jordan-w23/Project_BOO-E/Data logger/ESP32 docs/diagrams/datalogger.png

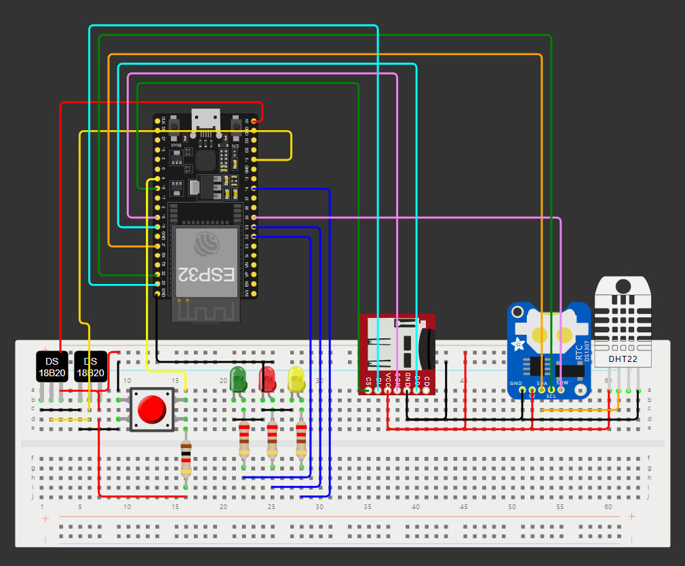
Data logger/ESP32 docs/diagrams/datalogger.png
