jordan-w23/Project_BOO-E/Data logger/ESP32 docs/diagrams/ESP32-DEV-CH340-USBC-003.jpg

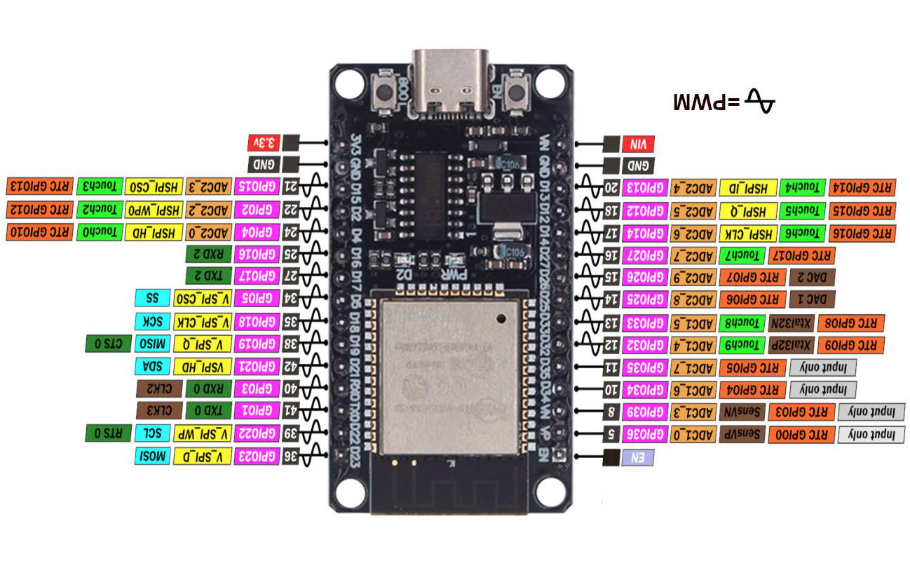
Data logger/ESP32 docs/diagrams/ESP32-DEV-CH340-USBC-003.jpg
