jordan-w23/Project_BOO-E/Data sheets/Rudder internal full.jpg

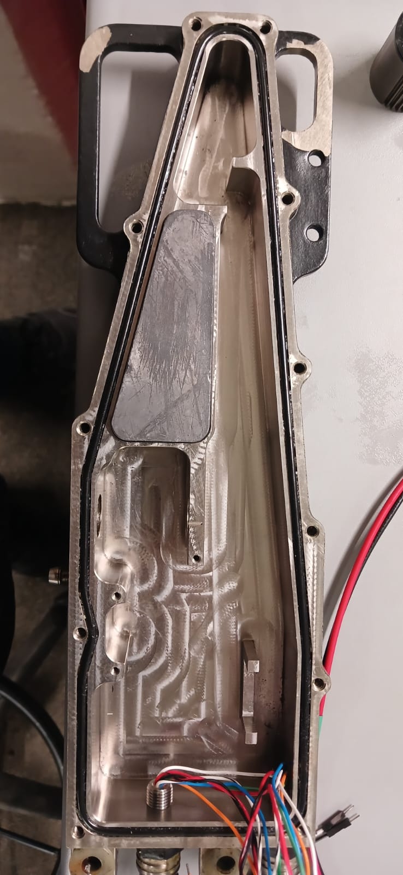
Data sheets/Rudder internal full.jpg
