jordan-w23/Project_BOO-E/Data sheets/Rudder internal ruller.jpg

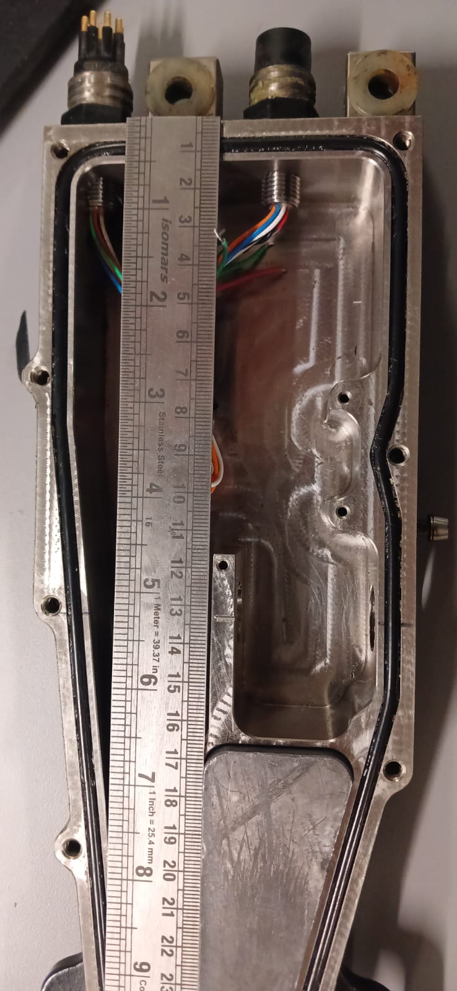
Data sheets/Rudder internal ruller.jpg
