jordan-w23/Project_BOO-E/Data sheets/Rudder internal.jpg

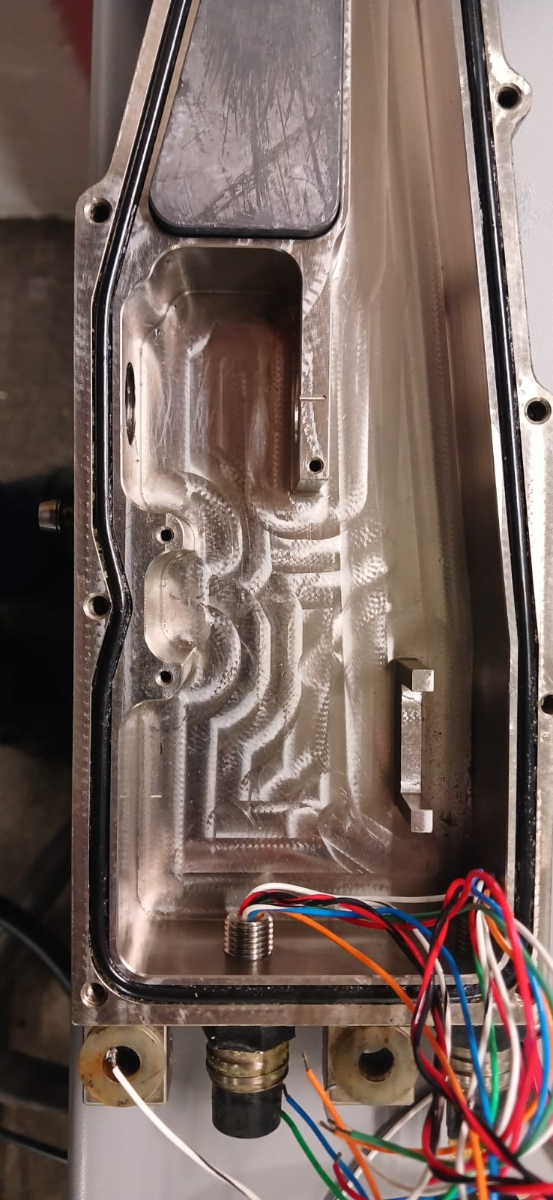
Data sheets/Rudder internal.jpg
