jordan-w23/Project_BOO-E/Pictures/BOO-E/IMG-20241016-WA0007.jpg

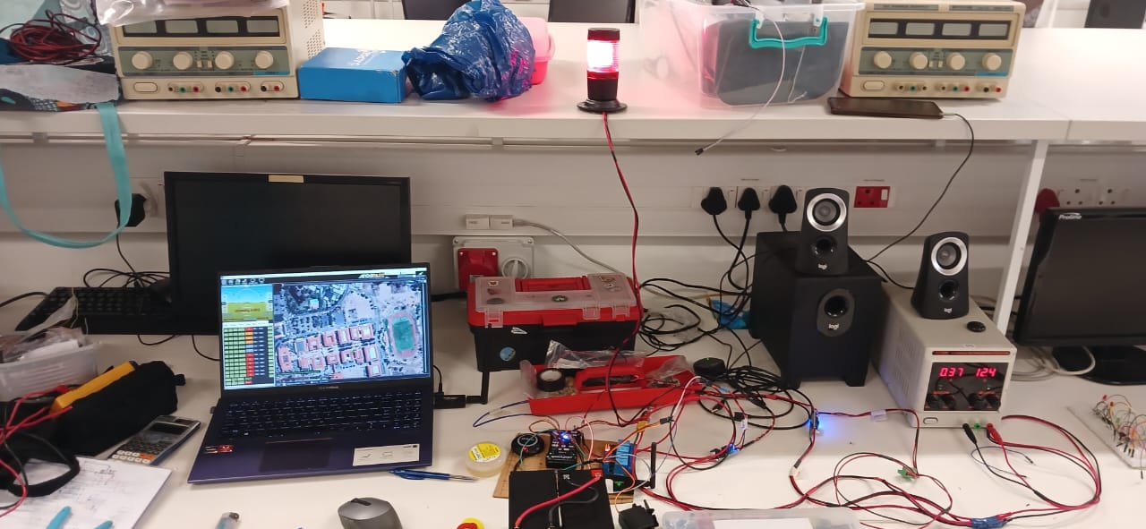
Pictures/BOO-E/IMG-20241016-WA0007.jpg
