jordan-w23/Project_BOO-E/Pictures/BOO-E/WhatsApp Image 2024-09-15 at 20.39.04_3f09f6b3.jpg

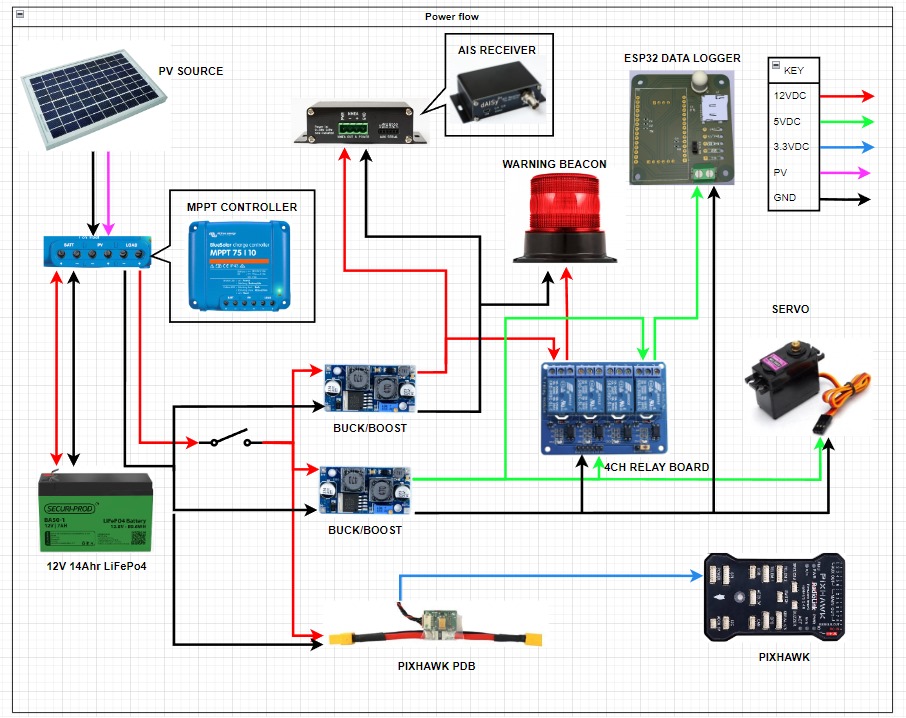
Pictures/BOO-E/WhatsApp Image 2024-09-15 at 20.39.04_3f09f6b3.jpg
