jordan-w23/Project_BOO-E/Pictures/BOO-E/WhatsApp Image 2024-10-16 at 18.33.03_7184913c.jpg

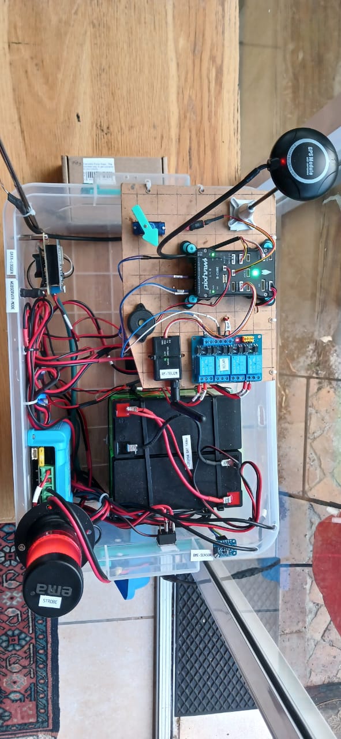
Pictures/BOO-E/WhatsApp Image 2024-10-16 at 18.33.03_7184913c.jpg
