jordan-w23/Project_BOO-E/Pictures/BOO-E/WhatsApp Image 2024-10-16 at 18.33.04_672b4f92.jpg

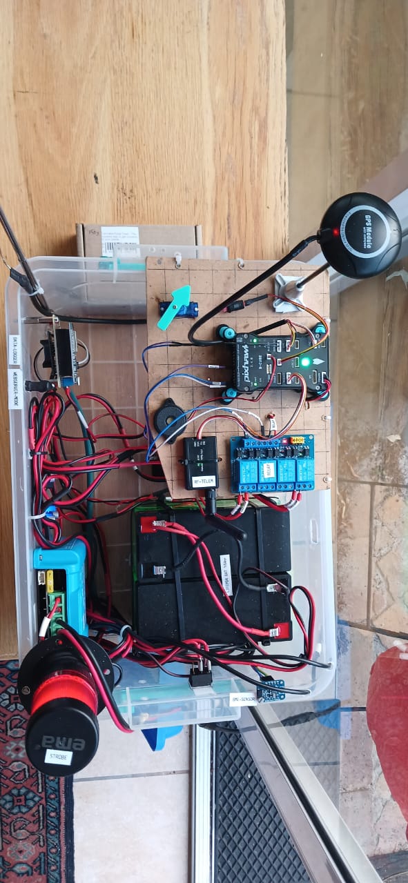
Pictures/BOO-E/WhatsApp Image 2024-10-16 at 18.33.04_672b4f92.jpg
