jordan-w23/Project_BOO-E/Pictures/BOO-E/WhatsApp Image 2024-10-17 at 18.35.57_54fe8b64.jpg

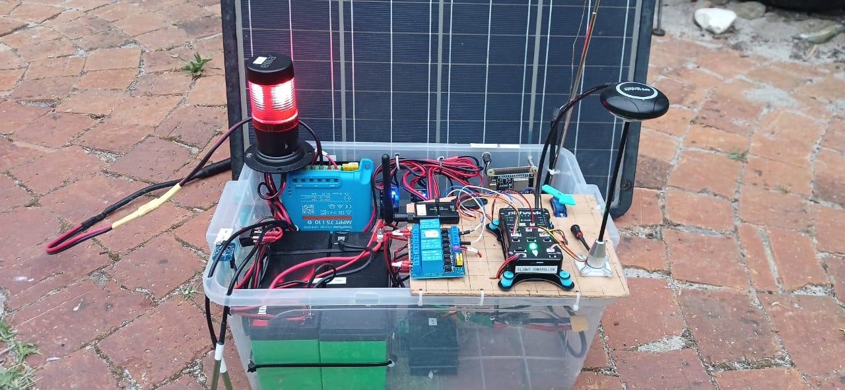
Pictures/BOO-E/WhatsApp Image 2024-10-17 at 18.35.57_54fe8b64.jpg
