jordan-w23/Project_BOO-E/Pictures/BOO-E/WhatsApp Image 2024-10-17 at 18.35.57_cdbaec98.jpg

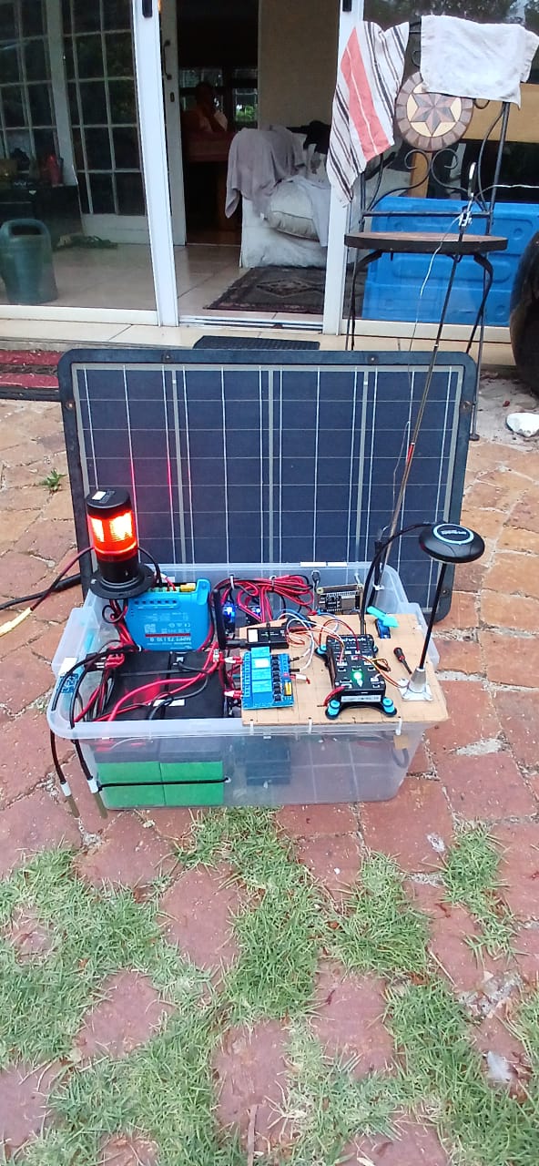
Pictures/BOO-E/WhatsApp Image 2024-10-17 at 18.35.57_cdbaec98.jpg
