jordan-w23/Project_BOO-E/Pictures/Data logger/IMG-20241016-WA0013.jpg

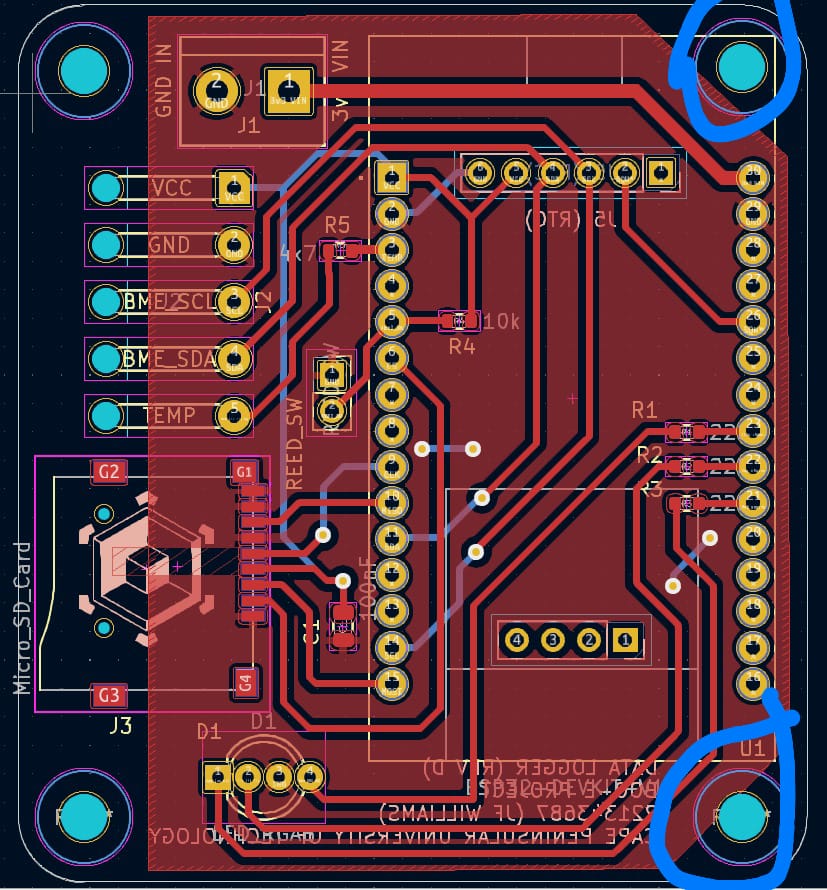
Pictures/Data logger/IMG-20241016-WA0013.jpg
