jordan-w23/Project_BOO-E/Pictures/GCS pixhawk/cf1507b16e4d5ccd977404383e6bbf5c3c93ac16.jpg

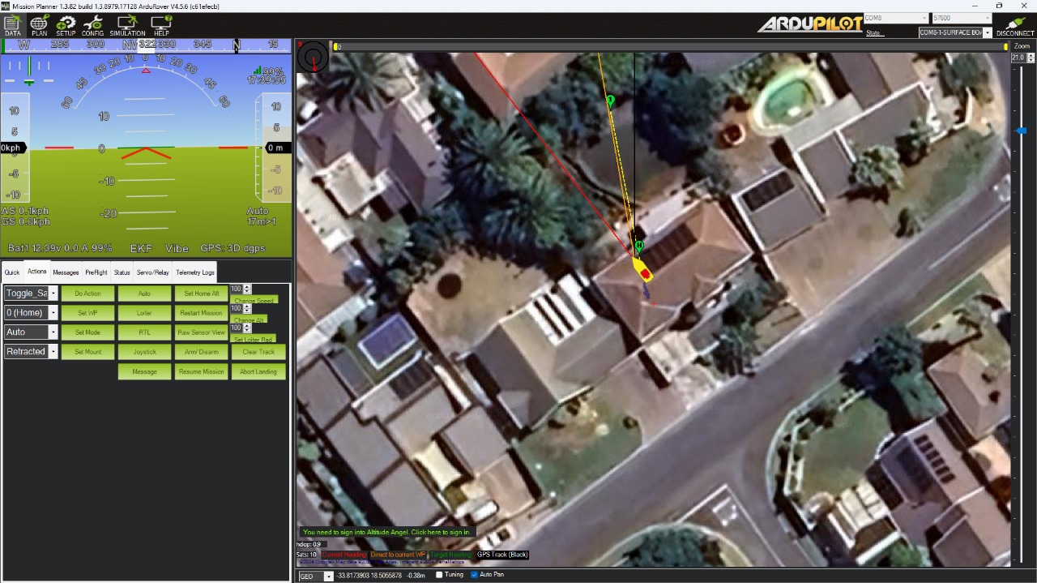
Pictures/GCS pixhawk/cf1507b16e4d5ccd977404383e6bbf5c3c93ac16.jpg
