jordan-w23/Project_BOO-E/Pictures/GCS pixhawk/IMG-20241016-WA0003.jpg

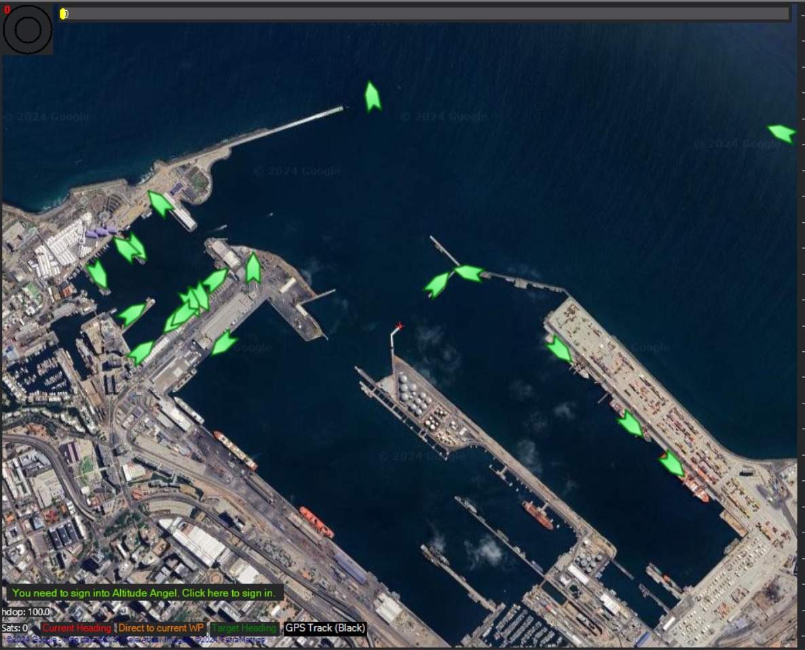
Pictures/GCS pixhawk/IMG-20241016-WA0003.jpg
