jordan-w23/Project_BOO-E/Pictures/GCS pixhawk/Left WP GSC.jpg

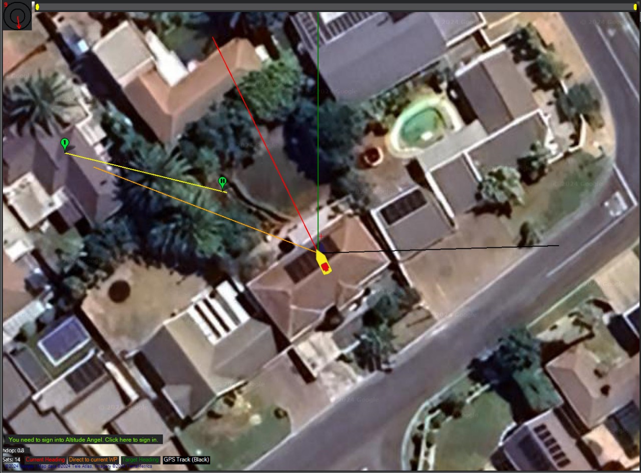
Pictures/GCS pixhawk/Left WP GSC.jpg
