jordan-w23/Project_BOO-E/Pictures/GCS pixhawk/Left WP view.jpg

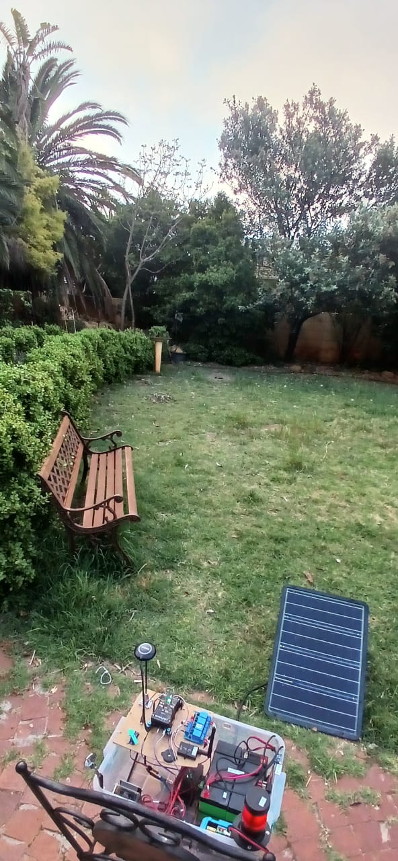
Pictures/GCS pixhawk/Left WP view.jpg
