jordan-w23/Project_BOO-E/Pictures/GCS pixhawk/left WP.jpg

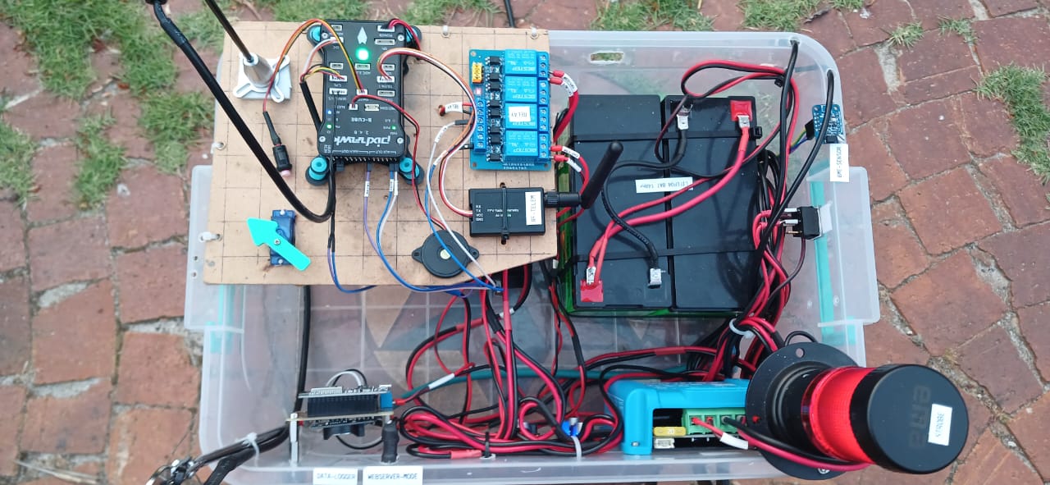
Pictures/GCS pixhawk/left WP.jpg
