jordan-w23/Project_BOO-E/Pictures/Solar/IMG-20240930-WA0002.jpg

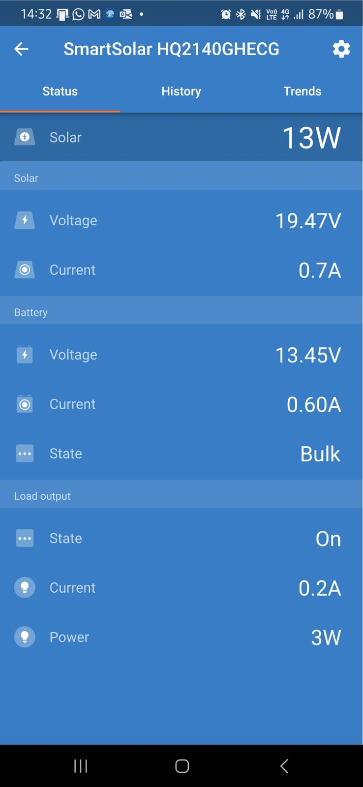
Pictures/Solar/IMG-20240930-WA0002.jpg
